GustavoMFreitas/PeNaLua/Assets/3ds/Obstacle/rock_008.obj

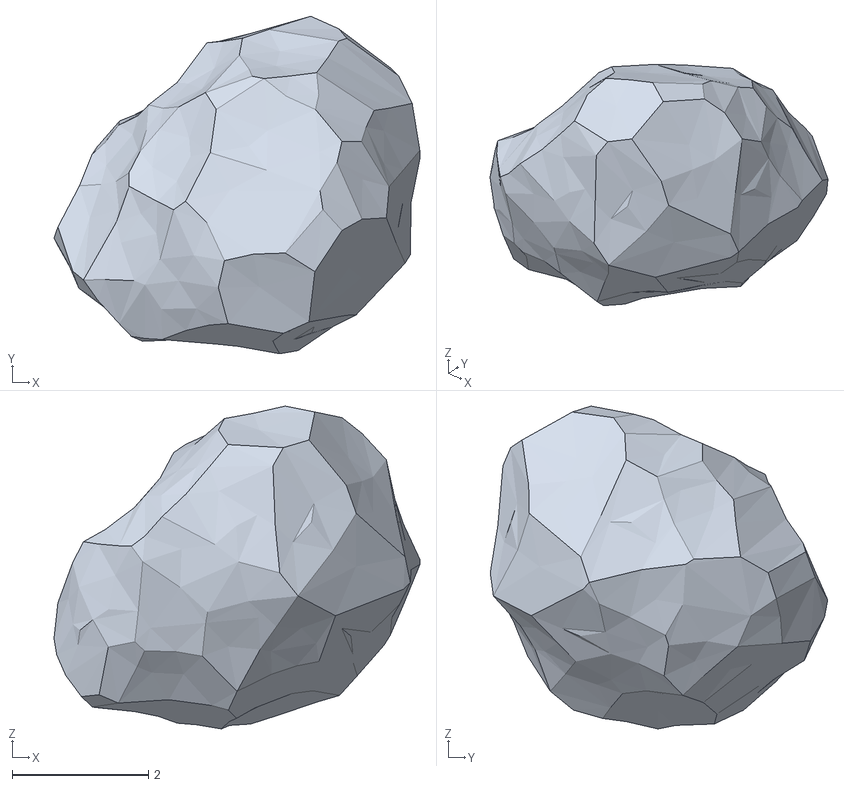
[picture p22: CAD file, 2023-11-30]
Assets/3ds/Obstacle/rock_008.obj
5.38 x 4.96 x 4.74
