GustavoMFreitas/PeNaLua/Assets/3ds/Obstacle/Ring.obj

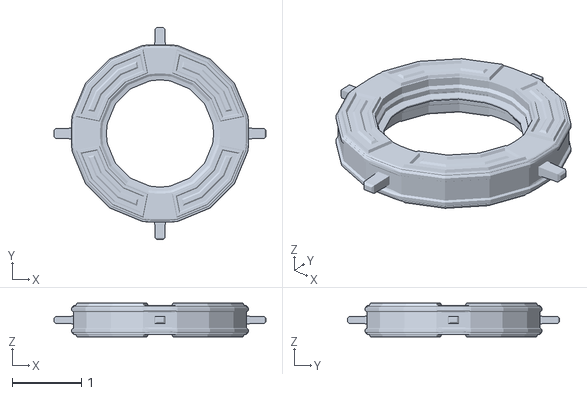
[picture p23: CAD file, 2023-11-30]
Assets/3ds/Obstacle/Ring.obj
3.05 x 3.05 x 0.488
